evernost/Qube/dev/qube_core/Core/Inc/push_button.h

// ============================================================================
// Module name    : push_button
// File name      : push_button.h
// Purpose        : 
// Author         : Quentin Biache
// Creation date  : June 18th, 2022
// ============================================================================

// Define to prevent recursive inclusion --------------------------------------
#ifndef __PUSH_BUTTON_H
#define __PUSH_BUTTON_H

#ifdef __cplusplus
extern "C" {
#endif

// Includes -------------------------------------------------------------------
#include <stdint.h>

// Defines --------------------------------------------------------------------
#define PB_L_MASK 0x1U
#define PB_R_MASK 0x2U
#define PB_U_MASK 0x4U
#define PB_D_MASK 0x8U

// Types ----------------------------------------------------------------------


// Functions prototypes -------------------------------------------------------

// Public


// Private


#ifdef __cplusplus
}
#endif

#endif // __PUSH_BUTTON_H
